Hansa2000/Digital_Kitchen_scale/Enclosure/moldable enclosure/sketches/front end.jpeg

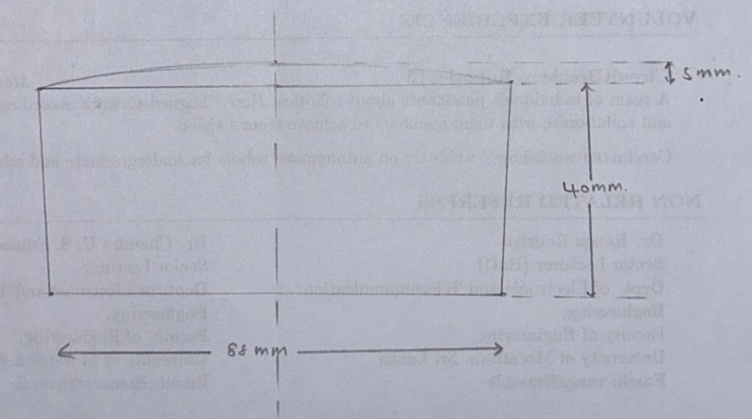
Enclosure/moldable enclosure/sketches/front end.jpeg
