Hansa2000/Digital_Kitchen_scale/Enclosure/moldable enclosure/sketches/front start.jpeg

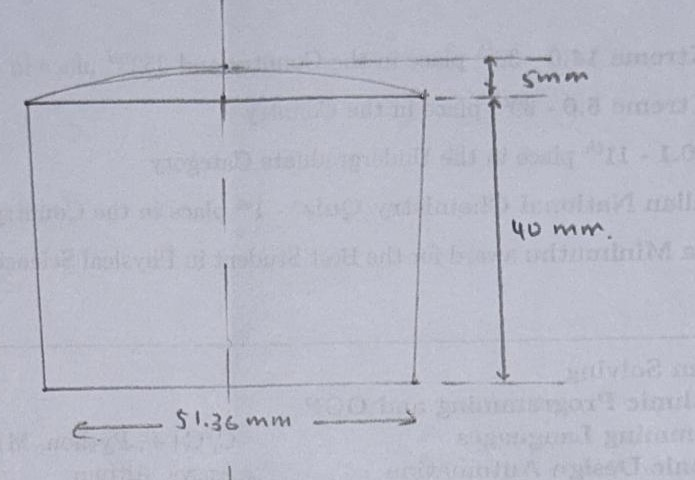
Enclosure/moldable enclosure/sketches/front start.jpeg
