Hansa2000/Digital_Kitchen_scale/Enclosure/moldable enclosure/sketches/fronts.jpeg

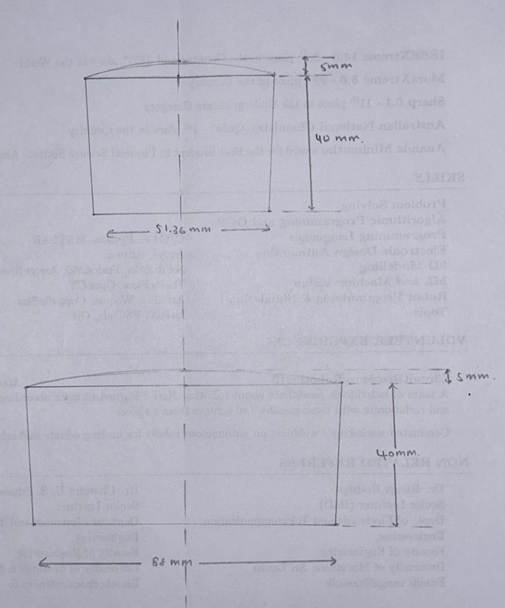
Enclosure/moldable enclosure/sketches/fronts.jpeg
