Hansa2000/Digital_Kitchen_scale/Enclosure/moldable enclosure/sketches/top view.jpeg

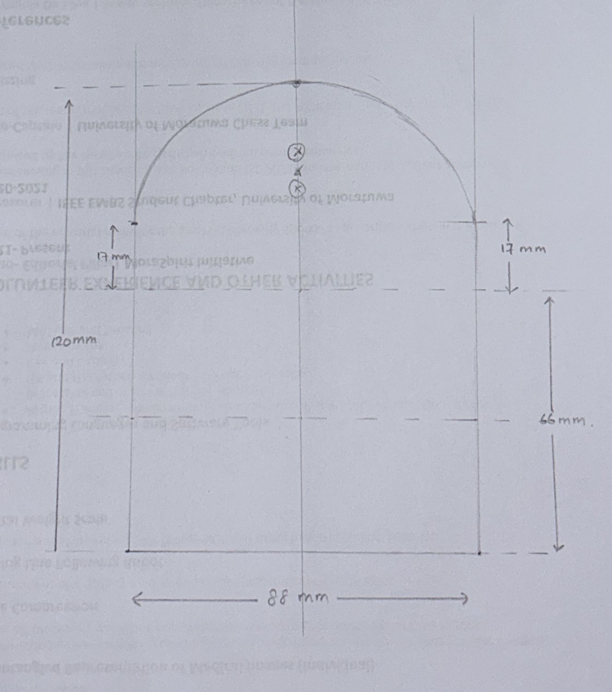
Enclosure/moldable enclosure/sketches/top view.jpeg
