Hansa2000/Digital_Kitchen_scale/Components/LED/kpa-3010cgck-led-1.snapshot.19/KPA-3010CGCK_2.132.png

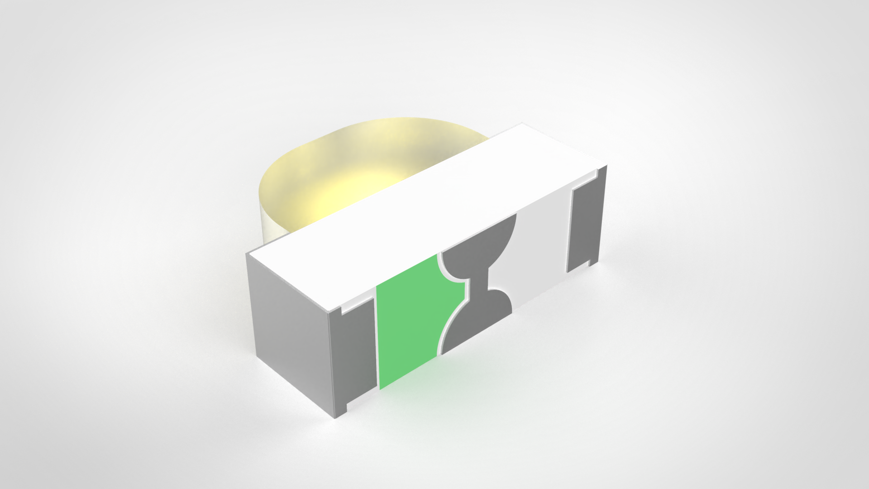
Components/LED/kpa-3010cgck-led-1.snapshot.19/KPA-3010CGCK_2.132.png
