Hansa2000/Digital_Kitchen_scale/Components/load cell/cheap-weight-sensor-1kg-2kg-3kg-5kg-10kg-20kg-1.snapshot.1/micro load cell FHDA.JPG

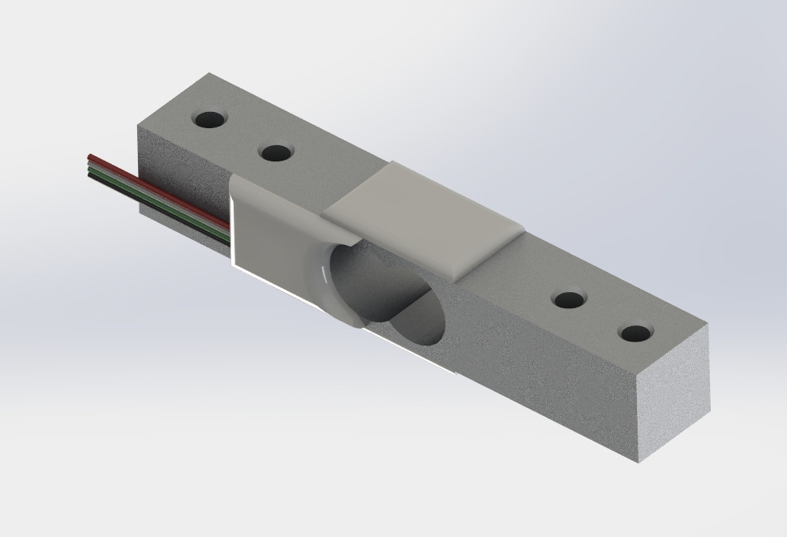
Components/load cell/cheap-weight-sensor-1kg-2kg-3kg-5kg-10kg-20kg-1.snapshot.1/micro load cell FHDA.JPG
