Hansa2000/Digital_Kitchen_scale/Components/47k res/LIB_RC0603FR-0747KL/RC0603FR-0747KL/3D/RC0603FR-0747KL.stp

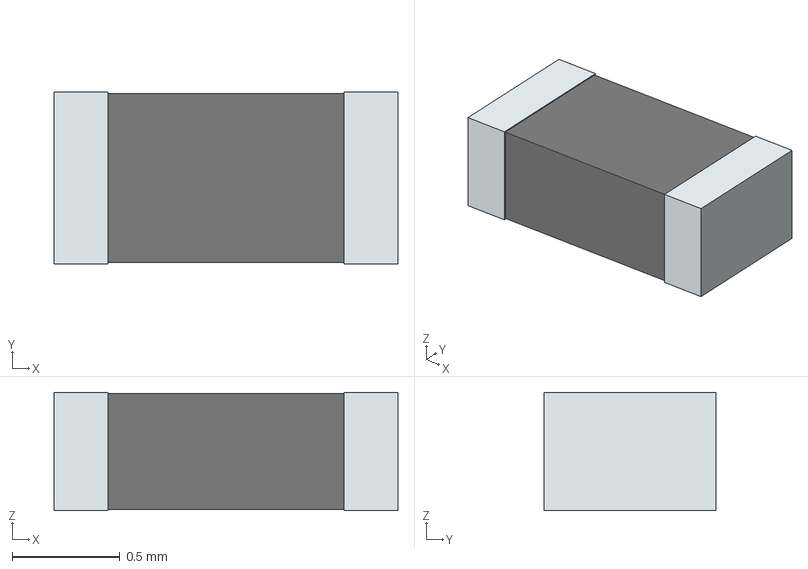
[picture p67: CAD file, 2023-08-13]
Components/47k res/LIB_RC0603FR-0747KL/RC0603FR-0747KL/3D/RC0603FR-0747KL.stp
1.60 x 0.8 x 0.55 mm
term1
term2
