Hansa2000/Digital_Kitchen_scale/Components/ceramic caps/0.1uF/LIB_C0805C104K5RAC7411/C0805C104K5RAC7411/3D/C0805C104K5RAC7411.stp

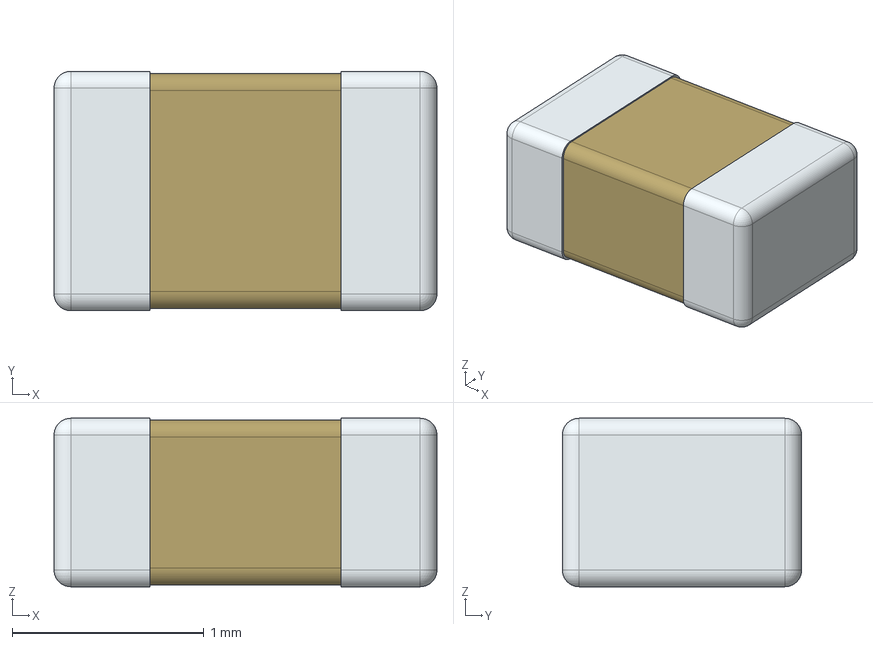
[picture p68: CAD file, 2023-08-13]
Components/ceramic caps/0.1uF/LIB_C0805C104K5RAC7411/C0805C104K5RAC7411/3D/C0805C104K5RAC7411.stp
2.00 x 1.25 x 0.88 mm
