Hansa2000/Digital_Kitchen_scale/Components/ceramic caps/4.7pF/LIB_C0805C479D3HACTU/C0805C479D3HACTU/3D/C0805C479D3HACTU.stp

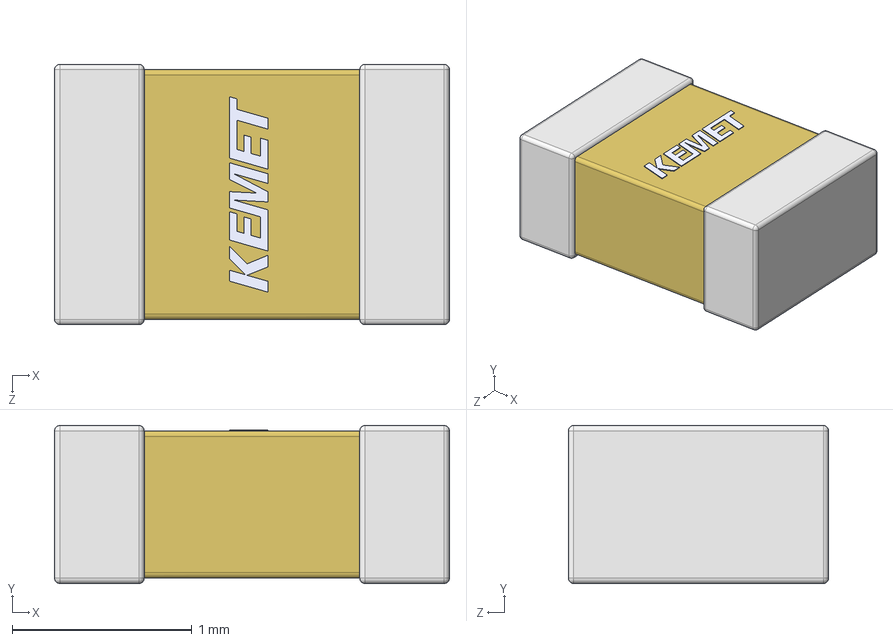
[picture p69: CAD file, 2023-08-13]
Components/ceramic caps/4.7pF/LIB_C0805C479D3HACTU/C0805C479D3HACTU/3D/C0805C479D3HACTU.stp
2.20 x 0.88 x 1.45 mm
