Hansa2000/Digital_Kitchen_scale/Components/ESP 12s/proteus/ESP-12S.step

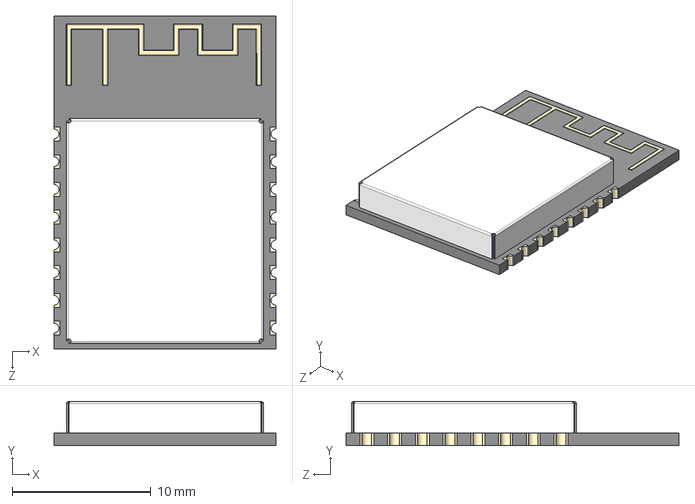
[picture p70: CAD file, 2023-08-13]
Components/ESP 12s/proteus/ESP-12S.step
16.0 x 3.20 x 24.0 mm
