Hansa2000/Digital_Kitchen_scale/Components/ESP12f/ESP-12F proteus/ESP-12F.step

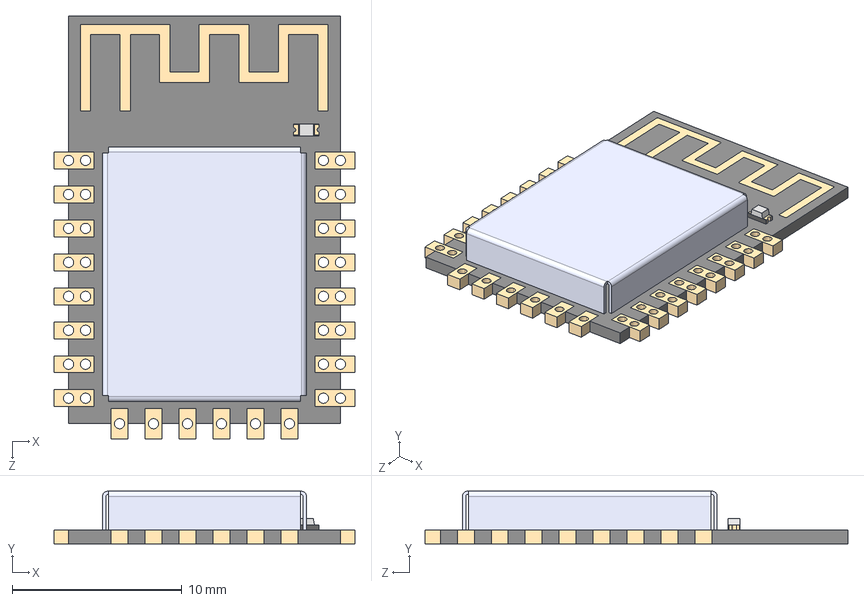
[picture p71: CAD file, 2023-08-13]
Components/ESP12f/ESP-12F proteus/ESP-12F.step
17.7 x 3.10 x 24.9 mm
