Hansa2000/Digital_Kitchen_scale/Components/jst header/B2B-XH-A-LF--SN---3DModel-STEP-269445.STEP

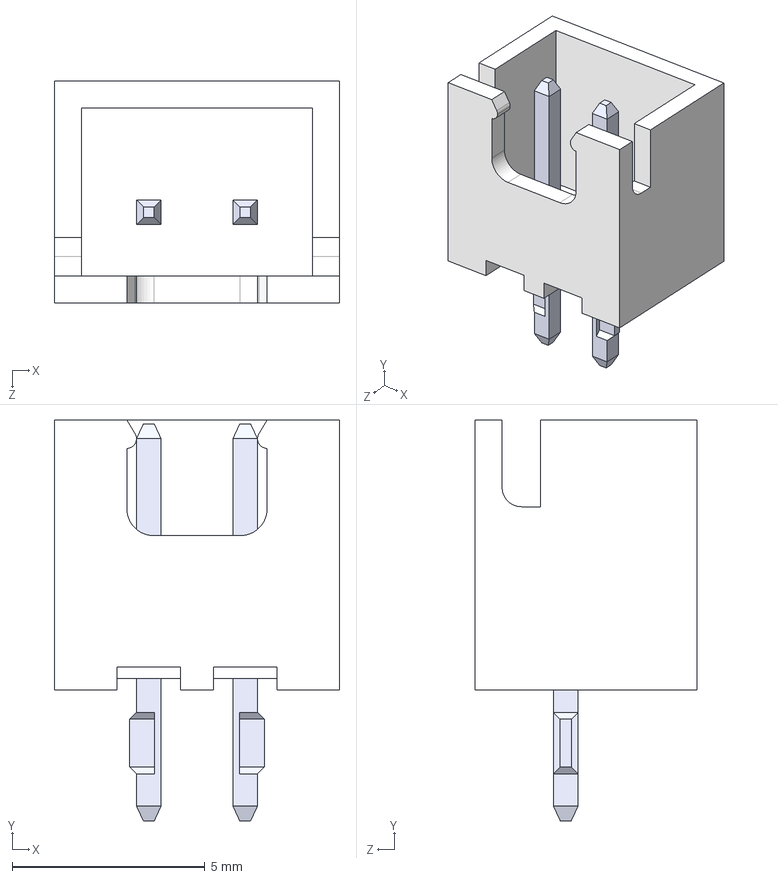
[picture p72: CAD file, 2023-08-13]
Components/jst header/B2B-XH-A-LF--SN---3DModel-STEP-269445.STEP
7.40 x 10.4 x 5.75 mm
