Hansa2000/Digital_Kitchen_scale/Components/LED/kpa-3010cgck-led-1.snapshot.19/KPA-3010CGCK-Base.SLDPRT

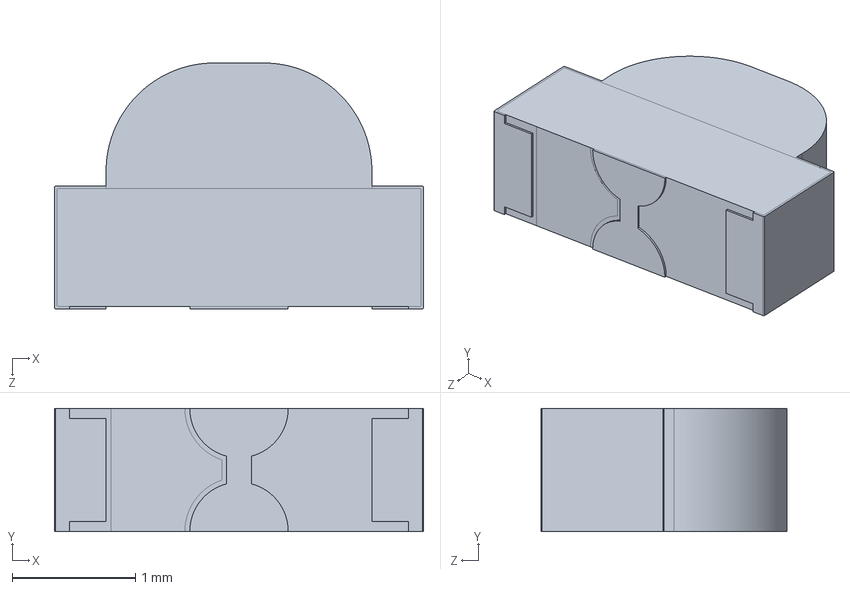
[picture p73: CAD file, 2023-08-13]
Components/LED/kpa-3010cgck-led-1.snapshot.19/KPA-3010CGCK-Base.SLDPRT
3.00 x 1.00 x 2.00 mm
