Hansa2000/Digital_Kitchen_scale/Components/load cell/cheap-weight-sensor-1kg-2kg-3kg-5kg-10kg-20kg-1.snapshot.1/weight sensor FHDA.STEP

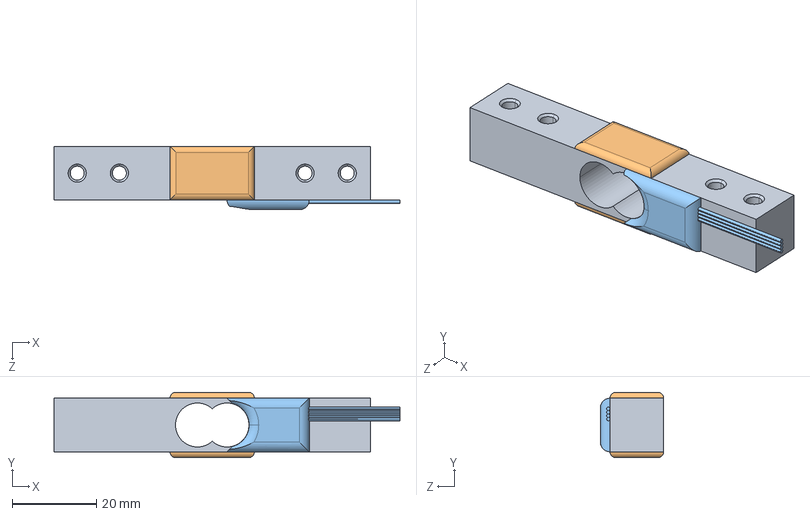
[picture p74: CAD file, 2023-08-13]
Components/load cell/cheap-weight-sensor-1kg-2kg-3kg-5kg-10kg-20kg-1.snapshot.1/weight sensor FHDA.STEP
82.0 x 15.5 x 15.0 mm
