Hansa2000/Digital_Kitchen_scale/Components/low power ldo/LIB_TC2117-3.3VDBTR/TC2117-3.3VDBTR/3D/TC2117-3.3VDBTR.stp

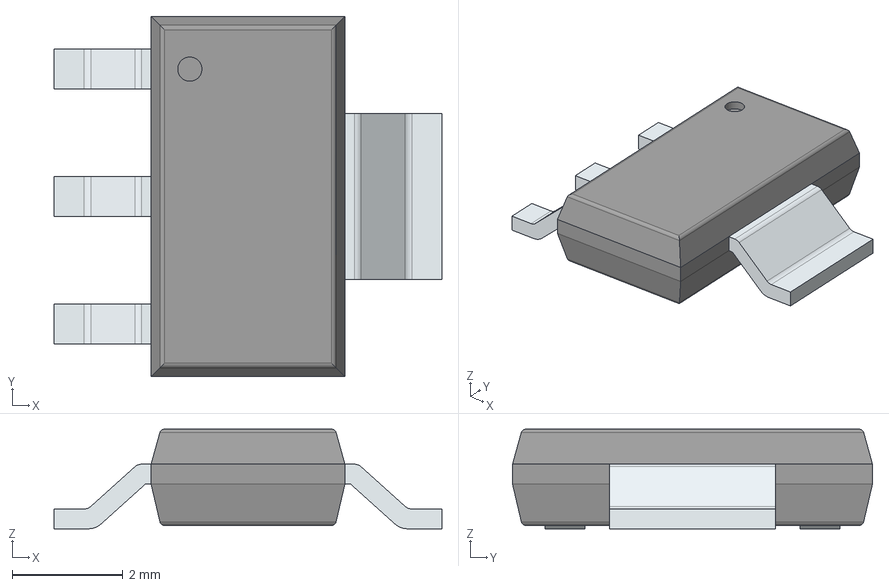
[picture p75: CAD file, 2023-08-13]
Components/low power ldo/LIB_TC2117-3.3VDBTR/TC2117-3.3VDBTR/3D/TC2117-3.3VDBTR.stp
7.00 x 6.50 x 1.80 mm
PinsArrayL
FilletPinR
