Hansa2000/Digital_Kitchen_scale/Components/oled/pantalla-oled-0-96-128x64-1.snapshot.7/Pantalla OLED 0.96'' 128x64.stp

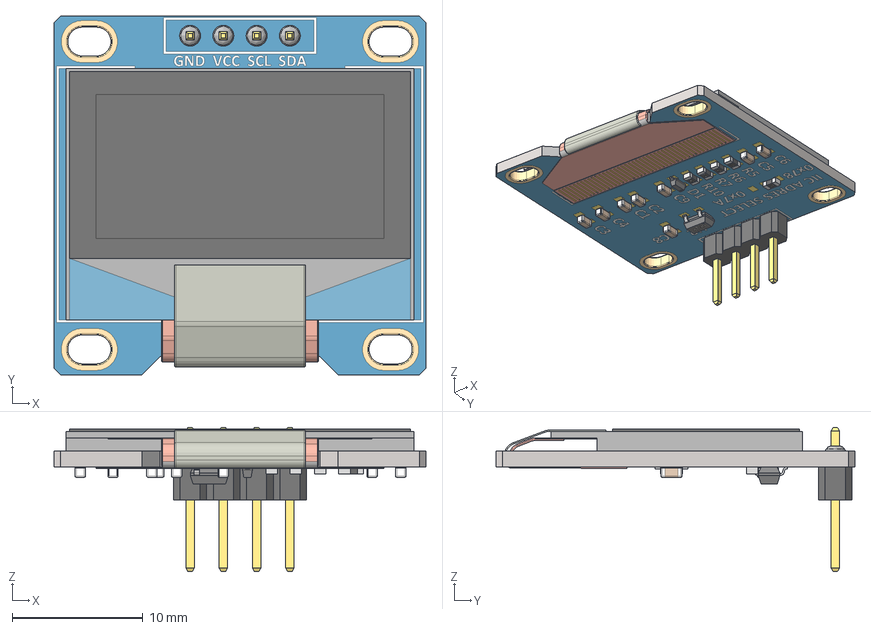
[picture p76: CAD file, 2023-08-13]
Components/oled/pantalla-oled-0-96-128x64-1.snapshot.7/Pantalla OLED 0.96'' 128x64.stp
28.4 x 27.4 x 11.0 mm
SOT-23_TOR
RES_CR16_MTK_1 x 4
RES_CR16_MTK
SOD323F_DIO
