Hansa2000/Digital_Kitchen_scale/Components/pin header male x 2/PARTserver22023041916434595217096d0b6156e/MTMM-101-15-T-D-650.stp

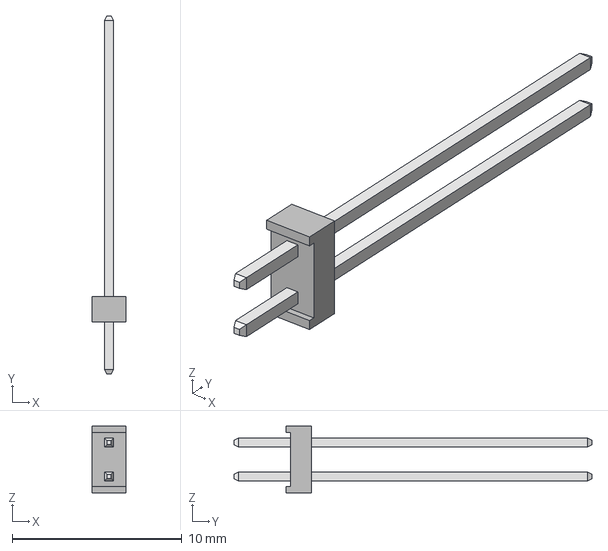
[picture p77: CAD file, 2023-08-13]
Components/pin header male x 2/PARTserver22023041916434595217096d0b6156e/MTMM-101-15-T-D-650.stp
2.00 x 21.1 x 3.94 mm
MTMM-101-15-T-D-650_body
MTMM-101-15-T-D-650_pins
