Hansa2000/Digital_Kitchen_scale/Components/pin header male/PARTserver22023041916385952416771d0b6156e/HTSW-101-07-H-S.stp

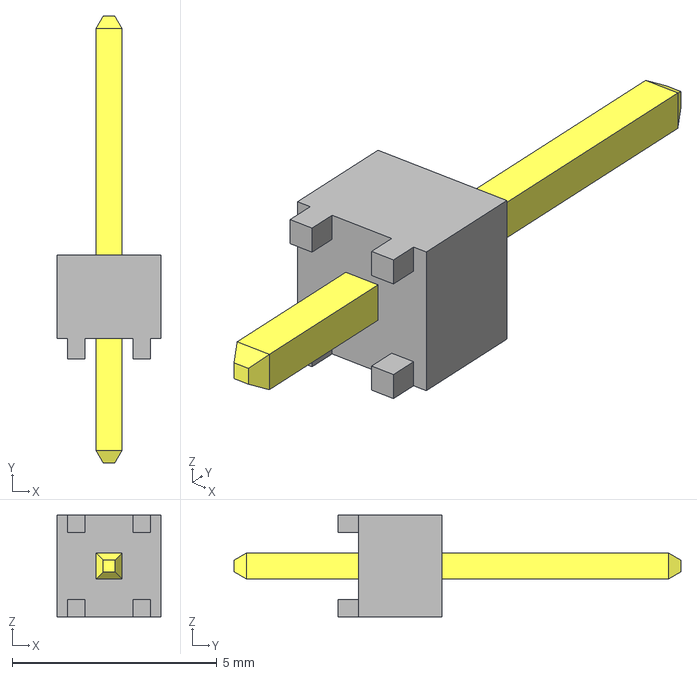
[picture p78: CAD file, 2023-08-13]
Components/pin header male/PARTserver22023041916385952416771d0b6156e/HTSW-101-07-H-S.stp
2.54 x 10.9 x 2.49 mm
T-1S6-07-HTSW-1--07-1-S
HTSW-101-07-H-S_body
