Hansa2000/Digital_Kitchen_scale/Components/tactile push button/tactile-switch-short-1.snapshot.1 (1)/tactileswitch-short/tactileswitch-short.STEP

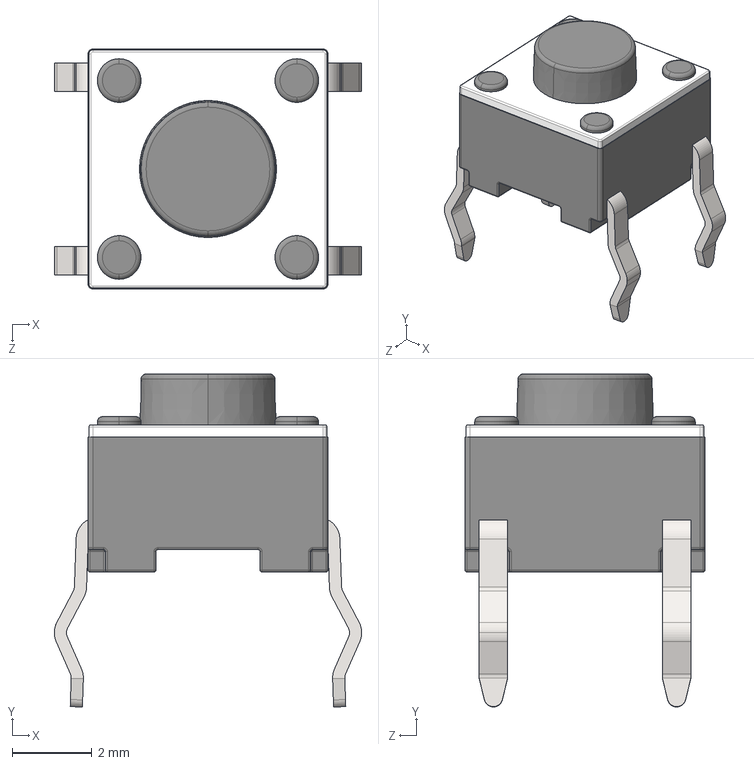
[picture p79: CAD file, 2023-08-13]
Components/tactile push button/tactile-switch-short-1.snapshot.1 (1)/tactileswitch-short/tactileswitch-short.STEP
7.69 x 8.33 x 6.01 mm
