Hansa2000/Digital_Kitchen_scale/Components/usb female port/USB3090-30-A--3DModel-STEP-56544.STEP

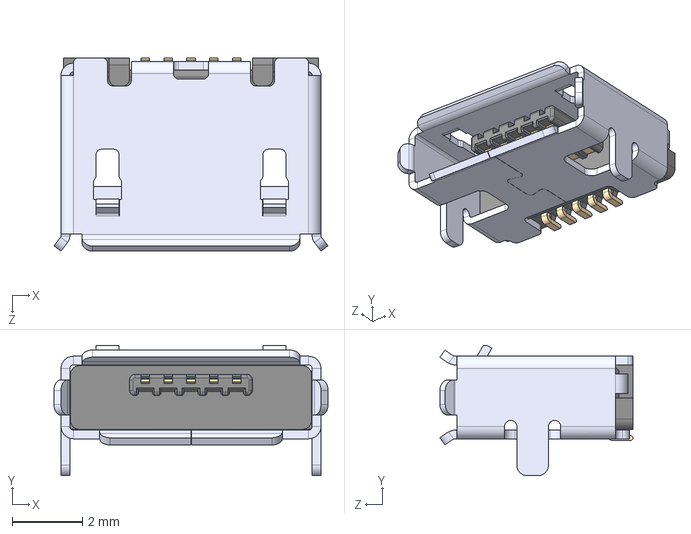
[picture p80: CAD file, 2023-08-13]
Components/usb female port/USB3090-30-A--3DModel-STEP-56544.STEP
7.80 x 3.71 x 5.50 mm
