Hansa2000/Digital_Kitchen_scale/Enclosure/moldable enclosure/top lid.SLDPRT

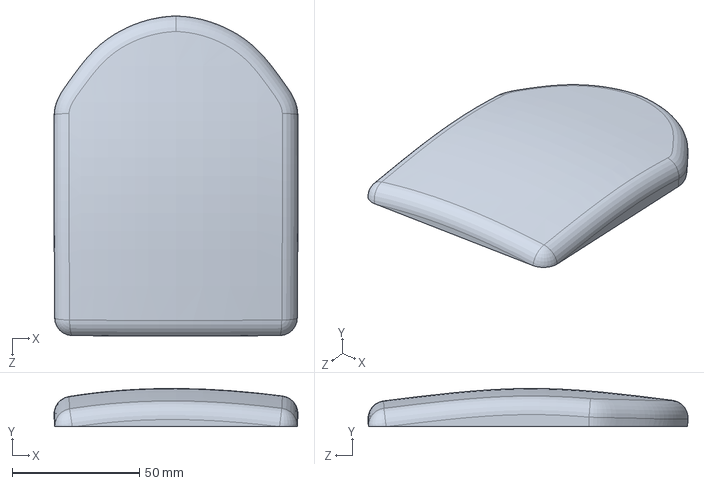
[picture p81: CAD file, 2023-08-13]
Enclosure/moldable enclosure/top lid.SLDPRT
95.8 x 15.0 x 125.7 mm
