Hansa2000/Digital_Kitchen_scale/Enclosure/version 5/files for laser cutting/tray.DXF

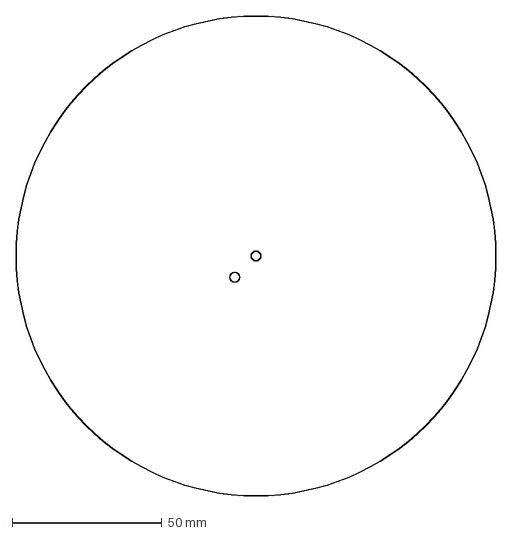
[picture p82: CAD file, 2023-08-13]
Enclosure/version 5/files for laser cutting/tray.DXF
160.0 x 160.0 mm
