Hansa2000/Digital_Kitchen_scale/Enclosure/version 5/files for printing/bottom part.STL

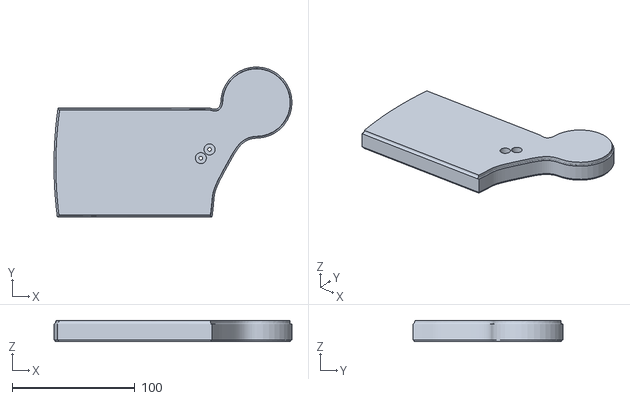
[picture p83: CAD file, 2023-08-13]
Enclosure/version 5/files for printing/bottom part.STL
193.9 x 122.2 x 17.3
