Hansa2000/Digital_Kitchen_scale/Enclosure/version 5/top part.SLDPRT

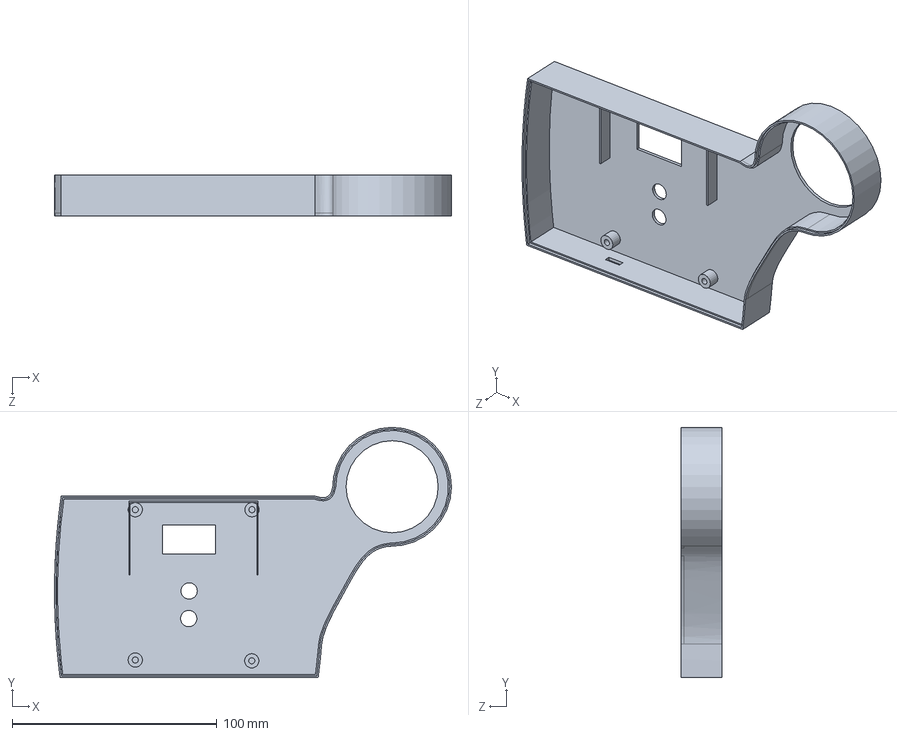
[picture p84: CAD file, 2023-08-13]
Enclosure/version 5/top part.SLDPRT
193.9 x 122.2 x 20.0 mm
