Hansa2000/Digital_Kitchen_scale/Enclosure/moldable enclosure/bottom box.SLDPRT

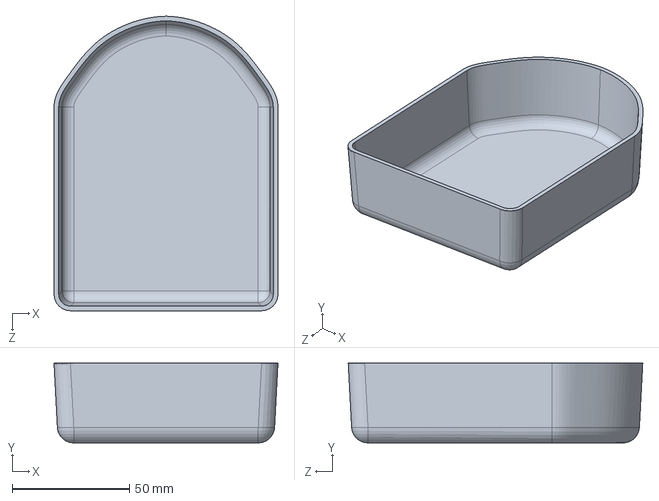
[picture p85: CAD file, 2023-08-13]
Enclosure/moldable enclosure/bottom box.SLDPRT
95.4 x 34.0 x 125.4 mm
