Hansa2000/Digital_Kitchen_scale/Enclosure/Raw desings/bottom lid.SLDPRT

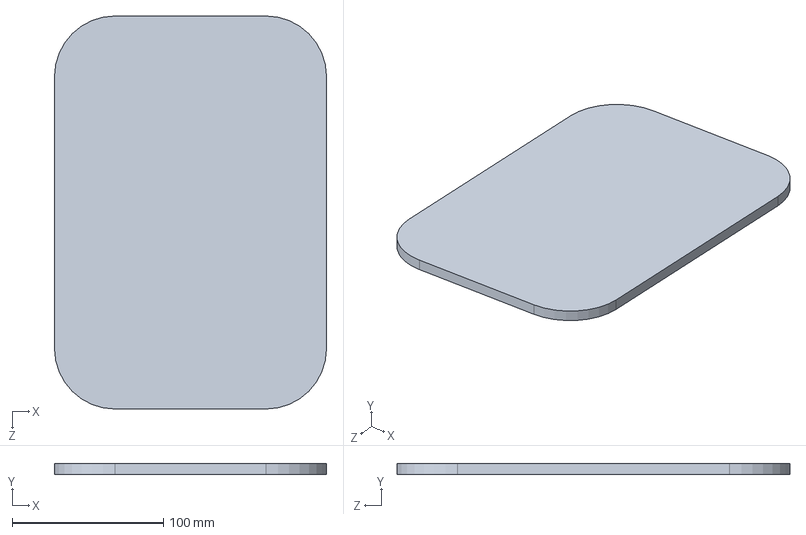
[picture p86: CAD file, 2023-08-13]
Enclosure/Raw desings/bottom lid.SLDPRT
180.0 x 7.50 x 260.0 mm
