Hansa2000/Digital_Kitchen_scale/Enclosure/version 5/enclosure.SLDPRT

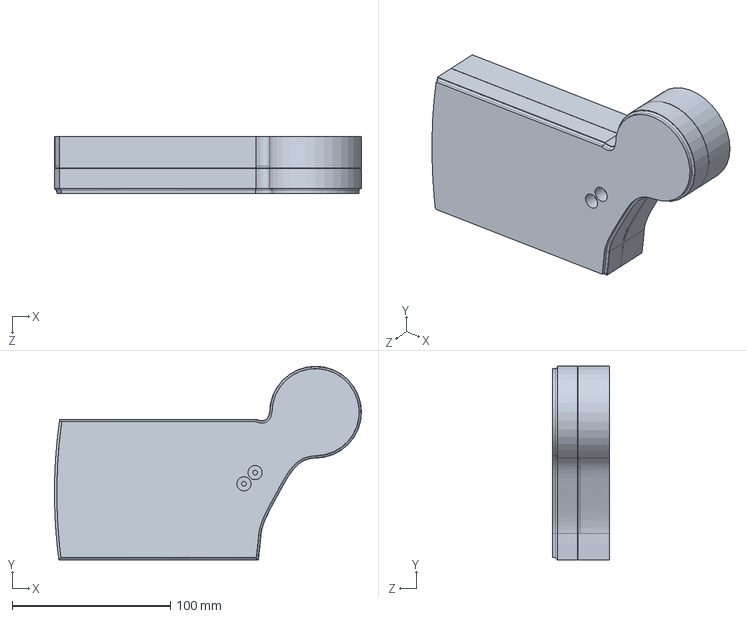
[picture p87: CAD file, 2023-08-13]
Enclosure/version 5/enclosure.SLDPRT
193.9 x 122.2 x 36.0 mm
