Hansa2000/Digital_Kitchen_scale/Enclosure/version 5/files for laser cutting/trayconnector.DXF

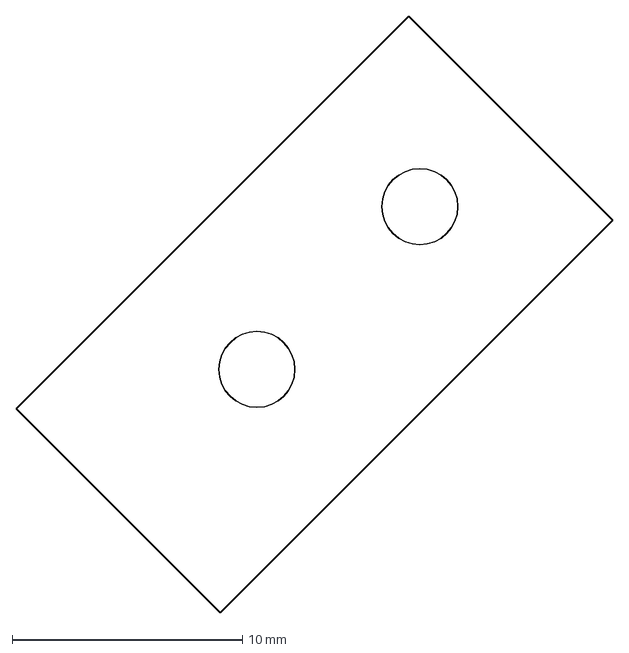
[picture p88: CAD file, 2023-08-13]
Enclosure/version 5/files for laser cutting/trayconnector.DXF
25.9 x 25.9 mm
