Hansa2000/Digital_Kitchen_scale/Enclosure/moldable enclosure/mybottom box.SLDPRT

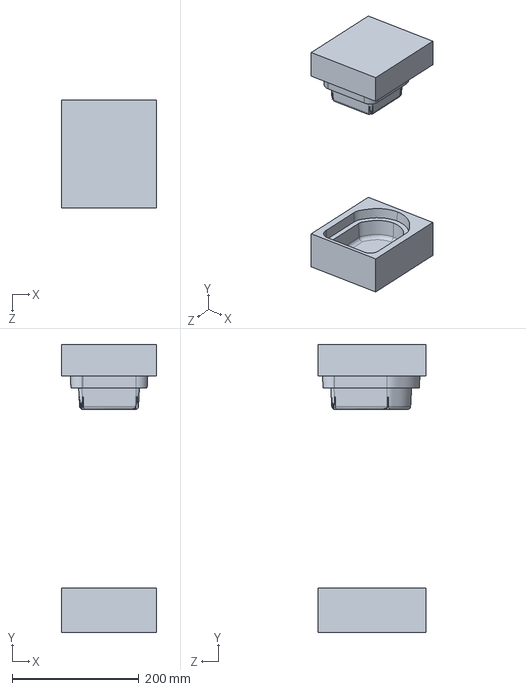
[picture p89: CAD file, 2023-08-13]
Enclosure/moldable enclosure/mybottom box.SLDPRT
150.0 x 453.9 x 170.0 mm
