Hansa2000/Digital_Kitchen_scale/Enclosure/version 5/files for printing/tray_v5.STL

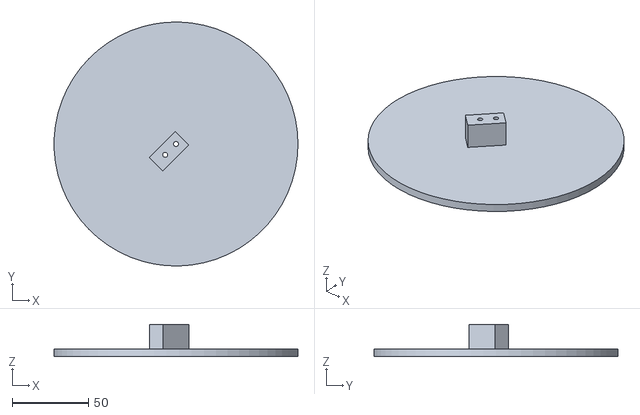
[picture p91: CAD file, 2023-08-13]
Enclosure/version 5/files for printing/tray_v5.STL
160.0 x 159.9 x 21.0
