Hansa2000/Digital_Kitchen_scale/Enclosure/version 5/Part12.SLDPRT

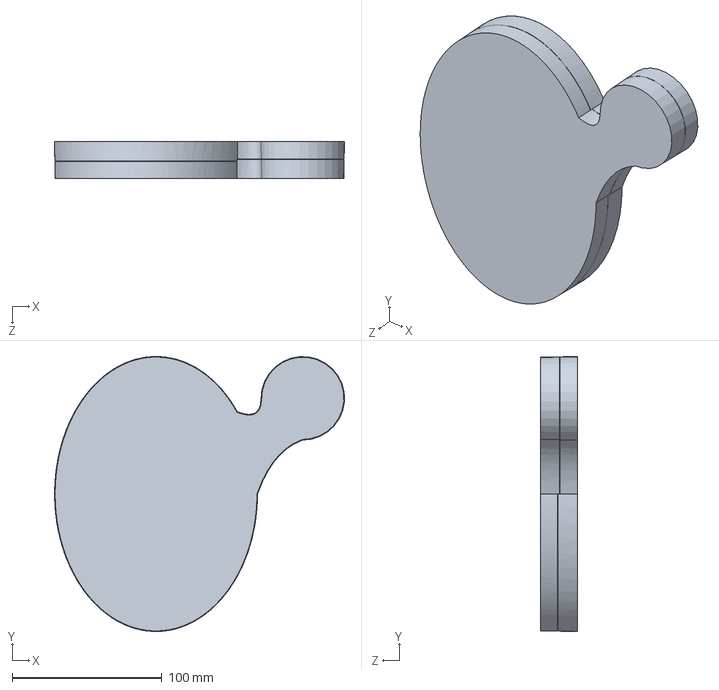
[picture p92: CAD file, 2023-08-13]
Enclosure/version 5/Part12.SLDPRT
194.0 x 184.0 x 25.0 mm
