Hansa2000/Digital_Kitchen_scale/Enclosure/Raw desings/tray.SLDPRT

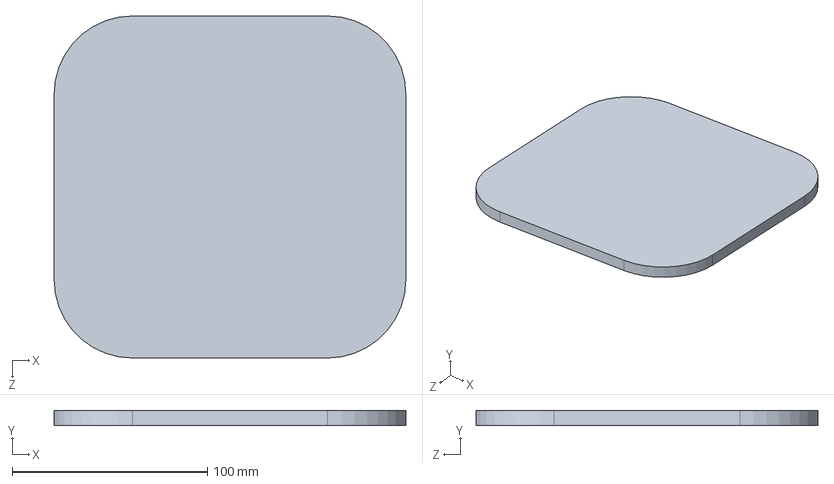
[picture p93: CAD file, 2023-08-13]
Enclosure/Raw desings/tray.SLDPRT
180.0 x 7.50 x 175.0 mm
