Hansa2000/Digital_Kitchen_scale/Enclosure/Raw desings/bottom mountSLDPRT.SLDPRT

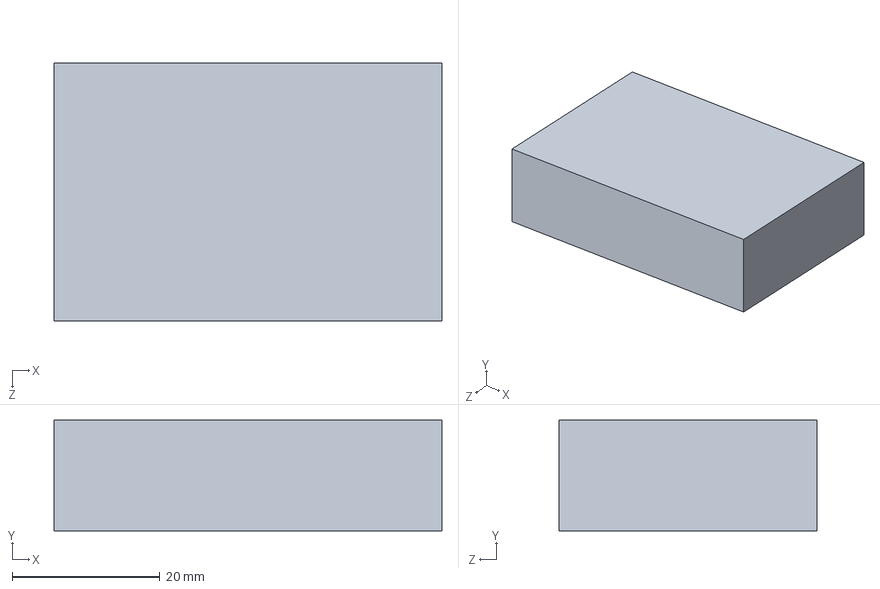
[picture p94: CAD file, 2023-08-13]
Enclosure/Raw desings/bottom mountSLDPRT.SLDPRT
52.6 x 15.0 x 35.0 mm
