Hansa2000/Digital_Kitchen_scale/Enclosure/Raw desings/pcb_version2.step

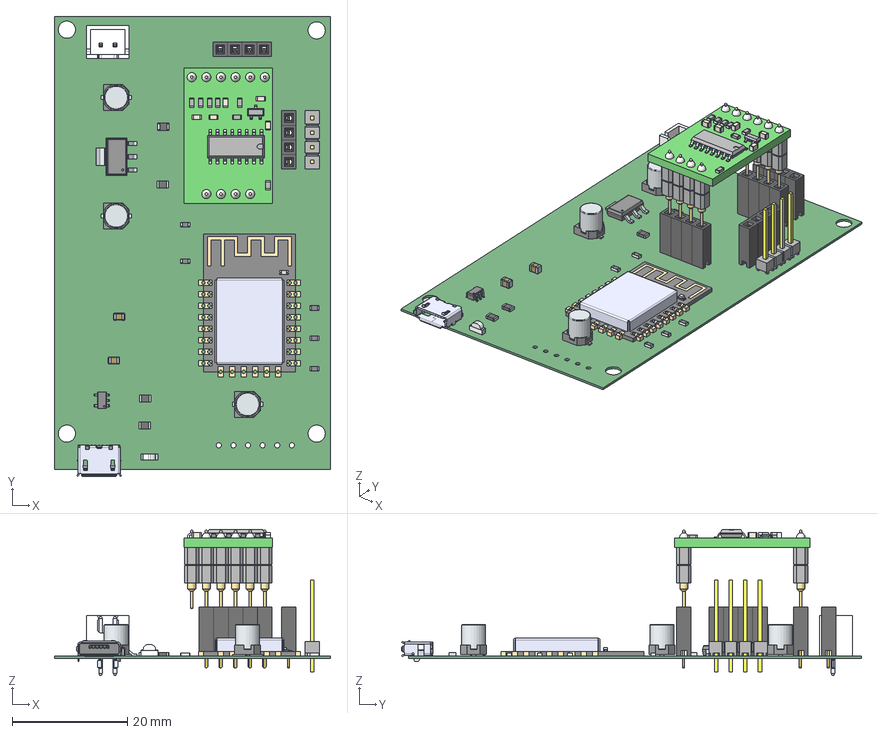
[picture p95: CAD file, 2023-08-13]
Enclosure/Raw desings/pcb_version2.step
48.0 x 80.0 x 25.4 mm
header x 16
pin x 16
USB3090-30-A--3DModel-STEP-56544
term1 x 3
term2 x 3
solidBody
Terminal
solidTop
CRG0603F10K_10 x 5
MCP73831T-5ACI_OT
KPA-3010CGCK-Base x 5
MTSW-104-22-S-420
MTSW-104-22-S-S-420_body
ESP-12F
Base x 6
Pin1Fillet x 6
Pin2Fillet x 6
PinsArrayL x 2
FilletPinR x 2
1x6 Male Header_001
1x4 Male Header_001
SOP-16L_001
1x4 Female Header_001
1x6 Female Header_001
0603 Resistor_001
0603 Capacitor_001
0603 Capacitor_002
0603 Capacitor_003
0603 Capacitor_004
0603 Capacitor_005
0603 Resistor_002
0603 Resistor_003
0603 Resistor_004
0603 Resistor_005
0603 Resistor_006
0603 Resistor_007
Surface Mount Transistor_001
