Hansa2000/Digital_Kitchen_scale/Enclosure/Raw desings/Body1.SLDPRT

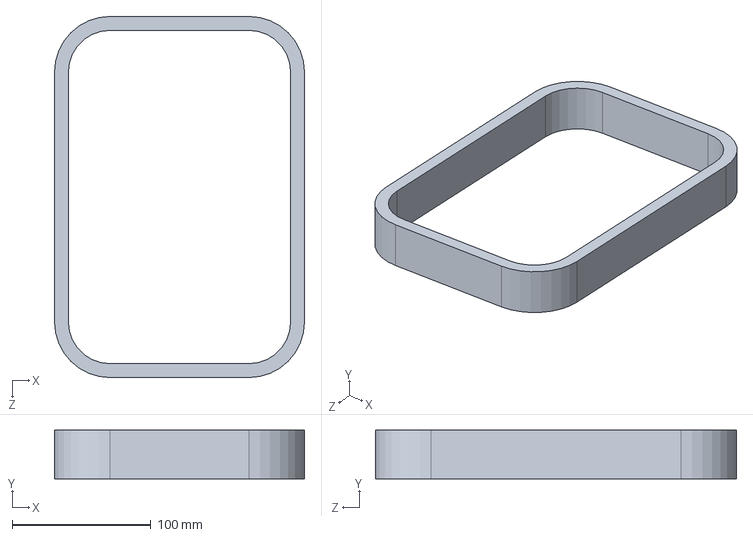
[picture p96: CAD file, 2023-08-13]
Enclosure/Raw desings/Body1.SLDPRT
180.0 x 35.0 x 260.0 mm
