Hansa2000/Digital_Kitchen_scale/Enclosure/Raw desings/top lid.STEP

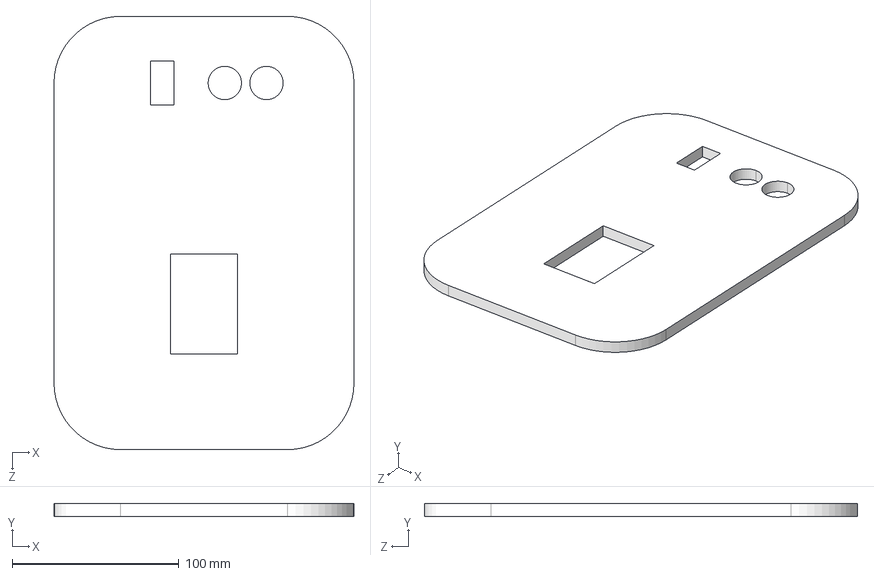
[picture p97: CAD file, 2023-08-13]
Enclosure/Raw desings/top lid.STEP
180.0 x 7.50 x 260.0 mm
