Hansa2000/Digital_Kitchen_scale/Enclosure/measurements second pcb.png

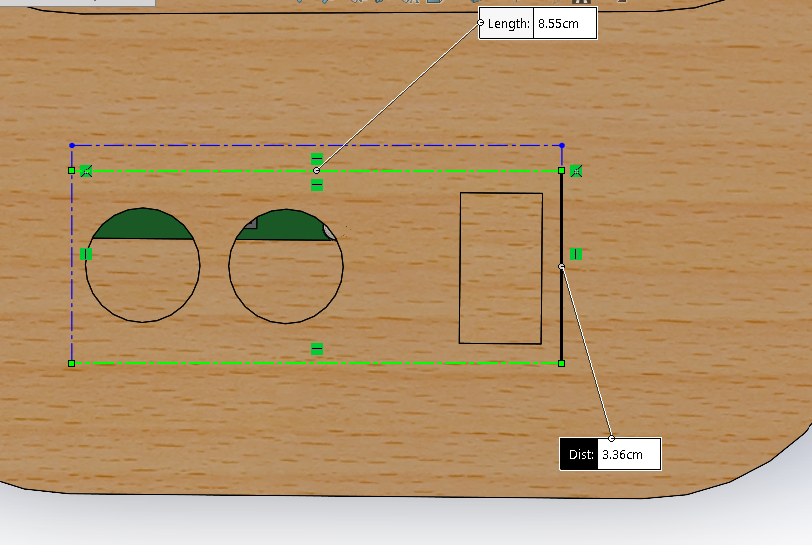
Enclosure/measurements second pcb.png
