Hansa2000/Digital_Kitchen_scale/Documentation/Schematics and PCB designing/source files/schematic_v1.pdf

# Micro-controller

# Headers

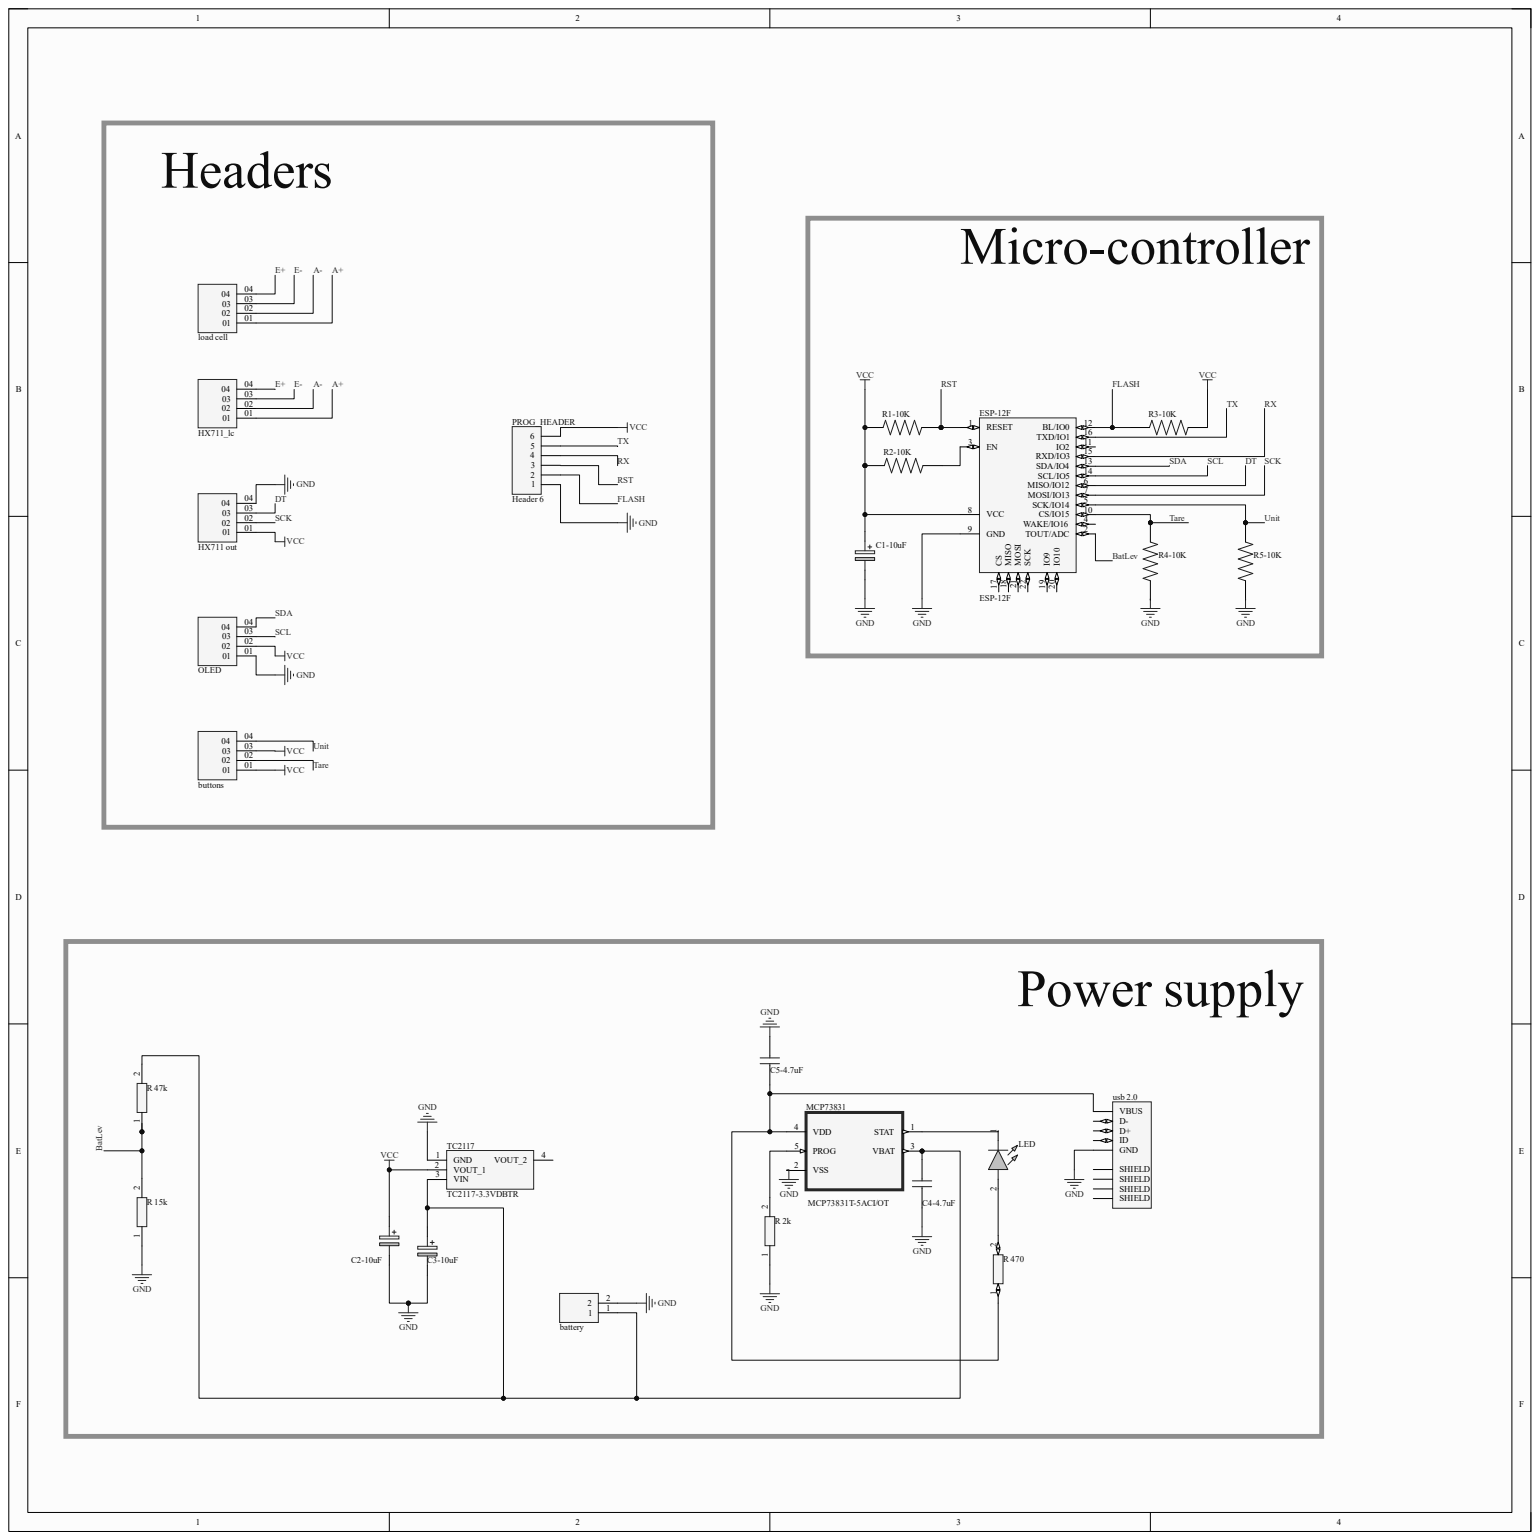
[picture p102: page 1]
RESET 1; VCC 8; GND 9; CS 17 MISO 18 MOSI 21; TXD/IO1; RXD/IO3; SDA/IO4; SCL/IO5; MISO/IO12; MOSI/IO13; SCK/IO14; WAKE/IO16; TOUT/ADC; 2 IO⁹ 19 IO¹⁰ 20 SCK 22; ESP-12F; VCC; GND; OLED; SDA; SCL; buttons; Tare; Unit; SCK; DT SCK; HX711 out; load cell; VBUS D- D+ ID GND; SHIELD SHIELD SHIELD SHIELD; usb 2.0; VDD 4; PROG 5; VSS 2; STAT; VBAT; MCP73831; MCP73831T-5ACI/OT; GND 1 VOUT_1 2 VIN 3; VOUT_2; TC2117-3.3VDBTR; LED; BatLev BatLev; Power supply; PROG_HEADER; Header 6; RST; FLASH; battery
